FreeVario/FreeVario/FreeVario/Src/fvconfig_hal.h

/*
 FreeVario http://FreeVario.org

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
 * config_hal.h
 *
 * Processor, channel and pin mappings
 * Only this file should needed to be configured when changing processors
 * Better use FV_ preamble to avoid conflicts
 */

#ifndef FVCONFIG_HAL_H_
#define FVCONFIG_HAL_H_
#ifdef __cplusplus
 extern "C" {
#endif
#include "stm32f4xx_hal.h"
#include "FreeRTOS.h"
extern UART_HandleTypeDef huart1;

 //Read the MPU UUID
#define STM32_UUID ((uint32_t *)0x1FFF7A10)

 //For the 1.1 version board that uses NPN transistor for the buzzer
#define FV_NPN_CHECK

 //FreeRtos Tasks enable
#define FV_DISPLAY
#define FV_SENSORS
#define FV_GPS
#define FV_SENDATA
#define FV_AUDIO
//#define FV_FANET
#define FV_LOGGER

 //DisplayRefresh every n seconds
#define FV_DISPLAYREFRESH 440

//Use GPS time instead of RTC
#define USEGPSDATETIME
//Logging is sync to the GPS but limited to 1 sec
#define GPSFREQUENCY 1

//Set RTC clock via GPS
#define SETRTCBYGPS

//Save config to SDCard
#define FV_CONFIGFILENAME "settings.cfg"
#define FV_CONFIGVERSION  4

//Board LED
#define FV_LED PB9_Pin
#define FV_LED_GPIO	GPIOB

//Audio baseline for buzzer
#define FV_TONEBASE 700

// Master I2C channel
/* Use this for the Baro and ACCL sensor
 * Configure: Fast mode 400
 * Disable the Analog filter if there are a lot of read errors
 * Setting digital filter to 2 (or higher) will help a lot
 */
#define FV_I2C hi2c1


//ACCL address
#define FV_ACCL_ADR 0x02 //F4 board pin is high

//GPS
/*
 * Speed: set for correct speed GPS
 * DMA: Enable DMA Channel with circular buffer
 * and set Global interrupt
 * Set polarity low and idle state to set
 */
#define FV_UARTGPS huart1


//BT
/*
 * Set Correct speed
 * DMA not needed
 */
#define FV_UARTBT huart3
#define FV_USARTBT USART3


//HW output for the speaker
#define FV_TONETMR htim1
#define FV_TONECHN TIM_CHANNEL_1
#define FV_TONEHALTMR TIM1



//LoRa modem spi
 #define FV_LoRa_SPI  hspi2


/*
 * Power management
 *
 */


//ADC for reading internal vBat Channel
//ADC1 needs to be enabled for it
//Continuous conversion mode set to enabled
#define FV_HALADC hadc1

/*
 * Buttons
 * Configure all buttons as GPIO_EXTI
 * to use the interrupt handler.
 * Use the same port
 */

#define FV_BTNOPTION GPIO_PIN_3
#define FV_BTNNEXT	GPIO_PIN_5 //B
#define FV_BTNPREV  GPIO_PIN_4 //B
#define FV_BRNPRT 	GPIOB







#endif /* FVCONFIG_HAL_H_ */
