FreeVario/FreeVario/FreeVario/Src/mpu6050/sd_hal_mpu6050.h

/*
 * sd_hal_mpu6050.h
 *
 *  Created on: Feb 19, 2016
 *      Author: Sina Darvishi
 */

#ifndef DRIVERS_MYLIB_SD_HAL_MPU6050_H_
#define DRIVERS_MYLIB_SD_HAL_MPU6050_H_

/*
 C++ detection
#ifdef __cplusplus
extern "C" {
#endif
*/

#include <../fvconfig.h>

/**
 * @defgroup SD_MPU6050_Macros
 * @brief    Library defines
 * @{
 */

/* Default I2C used */
//#ifndef MPU6050_I2C
//#define	MPU6050_I2C                    I2C1              /*!< Default I2C */
//#define MPU6050_I2C_PINSPACK           SD_I2C_PinsPack_1 /*!< Default I2C pinspack. Check @ref SD_I2C for more information */
//#endif

/* Default I2C clock */
#ifndef MPU6050_I2C_CLOCK
#define MPU6050_I2C_CLOCK              400000            /*!< Default I2C clock speed */
#endif

/**
 * @brief  Data rates predefined constants
 * @{
 */
#define SD_MPU6050_DataRate_8KHz       0   /*!< Sample rate set to 8 kHz */
#define SD_MPU6050_DataRate_4KHz       1   /*!< Sample rate set to 4 kHz */
#define SD_MPU6050_DataRate_2KHz       3   /*!< Sample rate set to 2 kHz */
#define SD_MPU6050_DataRate_1KHz       7   /*!< Sample rate set to 1 kHz */
#define SD_MPU6050_DataRate_500Hz      15  /*!< Sample rate set to 500 Hz */
#define SD_MPU6050_DataRate_250Hz      31  /*!< Sample rate set to 250 Hz */
#define SD_MPU6050_DataRate_125Hz      63  /*!< Sample rate set to 125 Hz */
#define SD_MPU6050_DataRate_100Hz      79  /*!< Sample rate set to 100 Hz */
/**
 * @}
 */

#define FCFG_3                  (1088)
#define FCFG_2                  (1066)
#define FCFG_1                  (1062)
#define FCFG_7                  (1073)


/**
 * @}
 */

/**
 * @defgroup SD_MPU6050_Typedefs
 * @brief    Library Typedefs
 * @{
 */

/**
 * @brief  MPU6050 can have 2 different slave addresses, depends on it's input AD0 pin
 *         This feature allows you to use 2 different sensors with this library at the same time
 */
typedef enum  {
	SD_MPU6050_Device_0 = 0x00, /*!< AD0 pin is set to low */
	SD_MPU6050_Device_1 = 0x02  /*!< AD0 pin is set to high */
} SD_MPU6050_Device;

/**
 * @brief  MPU6050 result enumeration
 */
typedef enum  {
	SD_MPU6050_Result_Ok = 0x00,          /*!< Everything OK */
	SD_MPU6050_Result_Error,              /*!< Unknown error */
	SD_MPU6050_Result_DeviceNotConnected, /*!< There is no device with valid slave address */
	SD_MPU6050_Result_DeviceInvalid       /*!< Connected device with address is not MPU6050 */
} SD_MPU6050_Result;

/**
 * @brief  Parameters for accelerometer range
 */
typedef enum  {
	SD_MPU6050_Accelerometer_2G = 0x00, /*!< Range is +- 2G */
	SD_MPU6050_Accelerometer_4G = 0x01, /*!< Range is +- 4G */
	SD_MPU6050_Accelerometer_8G = 0x02, /*!< Range is +- 8G */
	SD_MPU6050_Accelerometer_16G = 0x03 /*!< Range is +- 16G */
} SD_MPU6050_Accelerometer;

/**
 * @brief  Parameters for gyroscope range
 */
typedef enum {
	SD_MPU6050_Gyroscope_250s = 0x00,  /*!< Range is +- 250 degrees/s */
	SD_MPU6050_Gyroscope_500s = 0x01,  /*!< Range is +- 500 degrees/s */
	SD_MPU6050_Gyroscope_1000s = 0x02, /*!< Range is +- 1000 degrees/s */
	SD_MPU6050_Gyroscope_2000s = 0x03  /*!< Range is +- 2000 degrees/s */
} SD_MPU6050_Gyroscope;

/**
 * @brief  Main MPU6050 structure
 */
typedef struct  {
	/* Private */
	uint8_t Address;         /*!< I2C address of device. */
	float Gyro_Mult;         /*!< Gyroscope corrector from raw data to "degrees/s". Only for private use */
	float Acce_Mult;         /*!< Accelerometer corrector from raw data to "g". Only for private use */
	/* Public */
	int16_t Accelerometer_X; /*!< Accelerometer value X axis */
	int16_t Accelerometer_Y; /*!< Accelerometer value Y axis */
	int16_t Accelerometer_Z; /*!< Accelerometer value Z axis */
	int16_t Gyroscope_X;     /*!< Gyroscope value X axis */
	int16_t Gyroscope_Y;     /*!< Gyroscope value Y axis */
	int16_t Gyroscope_Z;     /*!< Gyroscope value Z axis */
	float   Temperature;       /*!< Temperature in degrees */
	//I2C_HandleTypeDef* I2Cx;
} SD_MPU6050;

/**
 * @brief  Interrupts union and structure
 */
typedef union {
	struct {
		uint8_t DataReady:1;       /*!< Data ready interrupt */
		uint8_t reserved2:2;       /*!< Reserved bits */
		uint8_t Master:1;          /*!< Master interrupt. Not enabled with library */
		uint8_t FifoOverflow:1;    /*!< FIFO overflow interrupt. Not enabled with library */
		uint8_t reserved1:1;       /*!< Reserved bit */
		uint8_t MotionDetection:1; /*!< Motion detected interrupt */
		uint8_t reserved0:1;       /*!< Reserved bit */
	} F;
	uint8_t Status;
} SD_MPU6050_Interrupt;


/**
 * @}
 */

/**
 * @defgroup SD_MPU6050_Functions
 * @brief    Library Functions
 * @{
 */

/**
 * @brief  Initializes MPU6050 and I2C peripheral
 * @param  *DataStruct: Pointer to empty @ref SD_MPU6050_t structure
 * @param  DeviceNumber: MPU6050 has one pin, AD0 which can be used to set address of device.
 *          This feature allows you to use 2 different sensors on the same board with same library.
 *          If you set AD0 pin to low, then this parameter should be SD_MPU6050_Device_0,
 *          but if AD0 pin is high, then you should use SD_MPU6050_Device_1
 *
 *          Parameter can be a value of @ref SD_MPU6050_Device_t enumeration
 * @param  AccelerometerSensitivity: Set accelerometer sensitivity. This parameter can be a value of @ref SD_MPU6050_Accelerometer_t enumeration
 * @param  GyroscopeSensitivity: Set gyroscope sensitivity. This parameter can be a value of @ref SD_MPU6050_Gyroscope_t enumeration
 * @retval Initialization status:
 *            - SD_MPU6050_Result_t: Everything OK
 *            - Other member: in other cases
 */
SD_MPU6050_Result SD_MPU6050_Init(I2C_HandleTypeDef* I2Cx,SD_MPU6050* DataStruct, SD_MPU6050_Device DeviceNumber, SD_MPU6050_Accelerometer AccelerometerSensitivity, SD_MPU6050_Gyroscope GyroscopeSensitivity);

/**
 * @brief  Sets gyroscope sensitivity
 * @param  *DataStruct: Pointer to @ref SD_MPU6050_t structure indicating MPU6050 device
 * @param  GyroscopeSensitivity: Gyro sensitivity value. This parameter can be a value of @ref SD_MPU6050_Gyroscope_t enumeration
 * @retval Member of @ref SD_MPU6050_Result_t enumeration
 */
SD_MPU6050_Result SD_MPU6050_SetGyroscope(I2C_HandleTypeDef* I2Cx,SD_MPU6050* DataStruct, SD_MPU6050_Gyroscope GyroscopeSensitivity);

/**
 * @brief  Sets accelerometer sensitivity
 * @param  *DataStruct: Pointer to @ref SD_MPU6050_t structure indicating MPU6050 device
 * @param  AccelerometerSensitivity: Gyro sensitivity value. This parameter can be a value of @ref SD_MPU6050_Accelerometer_t enumeration
 * @retval Member of @ref SD_MPU6050_Result_t enumeration
 */
SD_MPU6050_Result SD_MPU6050_SetAccelerometer(I2C_HandleTypeDef* I2Cx,SD_MPU6050* DataStruct, SD_MPU6050_Accelerometer AccelerometerSensitivity);

/**
 * @brief  Sets output data rate
 * @param  *DataStruct: Pointer to @ref SD_MPU6050_t structure indicating MPU6050 device
 * @param  rate: Data rate value. An 8-bit value for prescaler value
 * @retval Member of @ref SD_MPU6050_Result_t enumeration
 */
SD_MPU6050_Result SD_MPU6050_SetDataRate(I2C_HandleTypeDef* I2Cx,SD_MPU6050* DataStruct, uint8_t rate);


/**
 * @brief  Enables interrupts
 * @param  *DataStruct: Pointer to @ref SD_MPU6050_t structure indicating MPU6050 device
 * @retval Member of @ref SD_MPU6050_Result_t enumeration
 */
SD_MPU6050_Result SD_MPU6050_EnableInterrupts(I2C_HandleTypeDef* I2Cx,SD_MPU6050* DataStruct);

/**
 * @brief  Disables interrupts
 * @param  *DataStruct: Pointer to @ref SD_MPU6050_t structure indicating MPU6050 device
 * @retval Member of @ref SD_MPU6050_Result_t enumeration
 */
SD_MPU6050_Result SD_MPU6050_DisableInterrupts(I2C_HandleTypeDef* I2Cx,SD_MPU6050* DataStruct);

/**
 * @brief  Reads and clears interrupts
 * @param  *DataStruct: Pointer to @ref SD_MPU6050_t structure indicating MPU6050 device
 * @param  *InterruptsStruct: Pointer to @ref SD_MPU6050_Interrupt_t structure to store status in
 * @retval Member of @ref SD_MPU6050_Result_t enumeration
 */
SD_MPU6050_Result SD_MPU6050_ReadInterrupts(I2C_HandleTypeDef* I2Cx,SD_MPU6050* DataStruct, SD_MPU6050_Interrupt* InterruptsStruct);

/**
 * @brief  Reads accelerometer data from sensor
 * @param  *DataStruct: Pointer to @ref SD_MPU6050_t structure to store data to
 * @retval Member of @ref SD_MPU6050_Result_t:
 *            - SD_MPU6050_Result_Ok: everything is OK
 *            - Other: in other cases
 */
SD_MPU6050_Result SD_MPU6050_ReadAccelerometer(I2C_HandleTypeDef* I2Cx,SD_MPU6050* DataStruct);

/**
 * @brief  Reads gyroscope data from sensor
 * @param  *DataStruct: Pointer to @ref SD_MPU6050_t structure to store data to
 * @retval Member of @ref SD_MPU6050_Result_t:
 *            - SD_MPU6050_Result_Ok: everything is OK
 *            - Other: in other cases
 */
SD_MPU6050_Result SD_MPU6050_ReadGyroscope(I2C_HandleTypeDef* I2Cx,SD_MPU6050* DataStruct);

/**
 * @brief  Reads temperature data from sensor
 * @param  *DataStruct: Pointer to @ref SD_MPU6050_t structure to store data to
 * @retval Member of @ref SD_MPU6050_Result_t:
 *            - SD_MPU6050_Result_Ok: everything is OK
 *            - Other: in other cases
 */
SD_MPU6050_Result SD_MPU6050_ReadTemperature(I2C_HandleTypeDef* I2Cx,SD_MPU6050* DataStruct);

/**
 * @brief  Reads accelerometer, gyroscope and temperature data from sensor
 * @param  *DataStruct: Pointer to @ref SD_MPU6050_t structure to store data to
 * @retval Member of @ref SD_MPU6050_Result_t:
 *            - SD_MPU6050_Result_Ok: everything is OK
 *            - Other: in other cases
 */
SD_MPU6050_Result SD_MPU6050_ReadAll(I2C_HandleTypeDef* I2Cx,SD_MPU6050* DataStruct);

/**
 * @}
 */
SD_MPU6050_Result SD_MPU6050_SetOrientation(I2C_HandleTypeDef* I2Cx ,SD_MPU6050* DataStruct, unsigned short orient);
SD_MPU6050_Result mpu_write_mem(I2C_HandleTypeDef* I2Cx ,SD_MPU6050* DataStruct, unsigned short mem_addr, unsigned char *data);
/**
 * @}
 */

/**
 * @}
 */


#endif /* DRIVERS_MYLIB_SD_HAL_MPU6050_H_ */
