FreeVario/FreeVario/FreeVario/Src/FreeVario/settings.c

/*
 FreeVario http://FreeVario.org

 Copyright (c), FreeVario (http://freevario.org)
 This program is free software: you can redistribute it and/or modify
 it under the terms of the GNU General Public License as published by
 the Free Software Foundation, either version 3 of the License, or
 any later version. see <http://www.gnu.org/licenses/>
 */

#include "settings.h"
#include "freevario.h"

extern char SDPath[4]; /* SD logical drive path */
settings_t settings;
extern osMutexId confMutexHandle;
extern osMutexId sdCardMutexHandle;


/**
 * @brief  Save to SD, Mutexes must be claimed .
 * @param  argument: Not used
 * @retval None
 */
void saveConfigtoSD() {
    FIL confFile;

    if (activity.SDcardMounted) {
        FRESULT res;
        uint32_t byteswritten;
        if (f_open(&confFile, FV_CONFIGFILENAME, FA_CREATE_ALWAYS | FA_WRITE)
                != FR_OK) {
            /* 'STM32.TXT' file Open for write Error */
            //Error_Handler();
        } else {
            /* Write data to the text file */
            res = f_write(&confFile, &conf, sizeof(conf),
                    (void *) &byteswritten);

            if ((byteswritten == 0) || (res != FR_OK)) {
                /* 'STM32.TXT' file Write or EOF Error */
                //Error_Handler();
            } else {
                /* Close the open text file */
                f_close(&confFile);

            }

        }

    }
}

void loadConfigFromSD() {
    uint32_t bytesread;
    FIL confFile;
    FRESULT res;
    settings.SettingsFromSD = 0;

        if (f_open(&confFile, FV_CONFIGFILENAME, FA_READ) != FR_OK) {
            getDefaultConfig();
            saveConfigtoSD();

        } else {

            res = f_read(&confFile, &conf, sizeof(conf), (void *) &bytesread);


            if ((bytesread == 0) || (res != FR_OK)) {
                getDefaultConfig();
                saveConfigtoSD();
            } else if (conf.SaveVersion != FV_CONFIGVERSION) {
                getDefaultConfig();
                saveConfigtoSD();
            }else{
                settings.SettingsFromSD = 1;
            }

            f_close(&confFile);

        }



}

//load config by claiming a mutex
void loadConfigFromSDClaimMutex() {

    if ( xSemaphoreTake( confMutexHandle, ( TickType_t ) 200 ) == pdTRUE) {

        loadConfigFromSD();

        xSemaphoreGive(confMutexHandle);
    }

}

//save to SD card by claiming a mutex
void saveConfigtoSDClaimMutex() {

    if ( xSemaphoreTake( confMutexHandle, ( TickType_t ) 500 ) == pdTRUE) {

        saveConfigtoSD();

        xSemaphoreGive(confMutexHandle);
    }

}

void getDefaultConfig() {
    //version of the struct
    conf.SaveVersion = FV_CONFIGVERSION;

    //QNH value to calculate vario Altitude
    conf.qnePressure = 101325;

    // X 1000 Level to sound sink alarm
    conf.sinkAlarmLevel = -5000;

    //send data via serial port
    conf.SerialOut = true;

    //send data via bluetooth. BT uses power if not linked. Better to disable if not used.
    //BT will be available during startup, if the config menu is used, it will not be disabled.
    conf.SerialOutBT = true;

    //send data via attached ESP
    conf.SerialOutESP = false;

    // send data via USB for OTG
    conf.SerialOutUSB = true;

    // send ptas1 nmea, uses the gps channel (once every 100ms)
    conf.ptas1 = true;

    //send vario lxnav sentence
    conf.lxnav = false;

    //use the c-probe nmea sentence
    conf.pcprobe = true;

    //use custom nmea sentence
    conf.xcs = false;

    //low pass filter, the higher the number the slower the raw vario reading changes.
    conf.variosmooth = 20; //starting level

    // turn vario audio on or off
    conf.buzzer = true;

    //X 1000 Time Delay when speaker is muted during soar detection
    conf.SoarDeadBandTime = 30000;

    //X 1000 Value to detect vario movement (abs value needed)
    conf.advTriggerLevel = 200;

    // if vario level goes lower than advLowTrigger in this time, it will cause a trigger and increase conf.variosmooth.
    conf.advTriggerTime = 1000;

    // if no trigger occurs in this time frame, conf.variosmooth is reduced by 1,
    conf.advRelaxTime = 20000;

    // lowest level for conf.variosmooth
    conf.advMinSmooth = 10;

    // highest level for conf.variosmooth
    conf.advMaxSmooth = 30;

    // x1000 Glider sink rate
    conf.gliderSinkRate = -900;

    //save the last logbook number
    conf.lastLogNumber = 0;

    //GMT hours from median
    conf.gmtoffset = 2;


}
