FreeVario/FreeVario/FreeVario/Src/FreeVario/settings.h

/*
 FreeVario http://FreeVario.org

 Copyright (c), FreeVario (http://freevario.org)
 This program is free software: you can redistribute it and/or modify
 it under the terms of the GNU General Public License as published by
 the Free Software Foundation, either version 3 of the License, or
 any later version. see <http://www.gnu.org/licenses/>
 */

#ifndef SETTINGS_H_
#define SETTINGS_H_
#include "FreeRTOS.h"
#include "cmsis_os.h"
#include "stdbool.h"
#include "fatfs.h"
#include <stdlib.h>


#include "../fvconfig.h"

void saveConfigtoSD();
void loadConfigFromSD();
void getDefaultConfig();
void loadConfigFromSDClaimMutex();
void saveConfigtoSDClaimMutex();

typedef struct {
    int SaveVersion;
    int qnePressure;
    int sinkAlarmLevel;
    bool SerialOut;
    bool SerialOutBT;
    bool SerialOutESP;
    bool SerialOutUSB;
    bool ptas1;
    bool lxnav;
    bool pcprobe; //
    bool xcs; //
    int variosmooth;
    bool buzzer;
    int SoarDeadBandTime;
    int advTriggerLevel;
    int advTriggerTime;
    int advRelaxTime;
    int advMinSmooth;
    int advMaxSmooth;
    int gliderSinkRate;
    int lastLogNumber;
    int gmtoffset;

} conf_t;

extern conf_t conf;

typedef enum {

    s_SaveVersion = 2, s_qnePressure = 2

} Settings_headers;


typedef struct {
    uint8_t SettingsFromSD; //flag if the settings were loaded from SD

}settings_t;

extern settings_t settings;

#endif /* SETTINGS_H_ */
